japinkerton/3D-Printed-Copy-Stand/Photos/Completed_Copy_Stand.jpeg

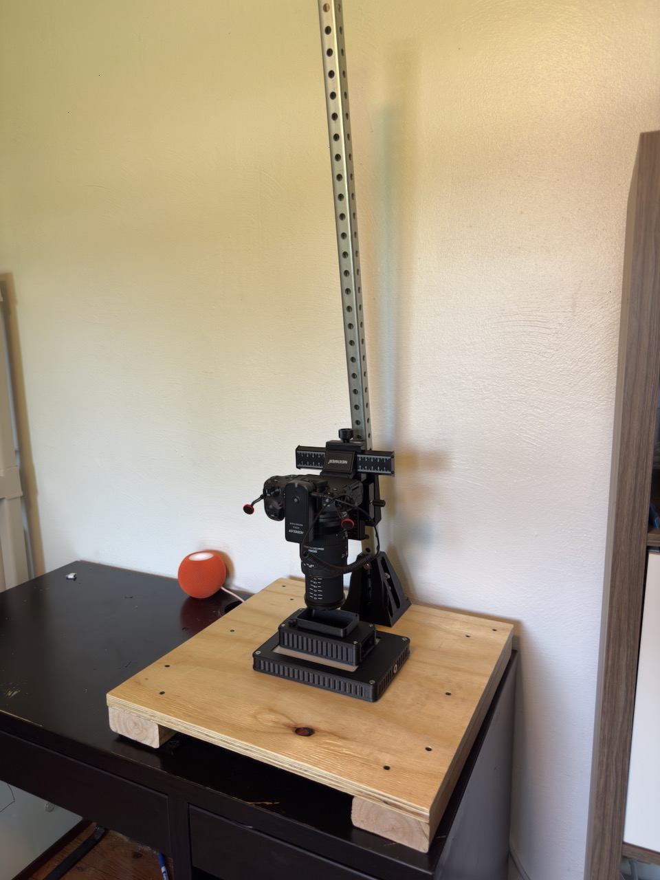
Photos/Completed_Copy_Stand.jpeg
